BrainOnFire/SNAP_Project_Files/SNAP Project Code/STM32_WPAN/App/custom_app.h

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

/* Define to prevent recursive inclusion -------------------------------------*/
#ifndef CUSTOM_APP_H
#define CUSTOM_APP_H

#ifdef __cplusplus
extern "C" {
#endif

/* Includes ------------------------------------------------------------------*/

/* Exported types ------------------------------------------------------------*/
typedef enum
{
  CUSTOM_CONN_HANDLE_EVT,
  CUSTOM_DISCON_HANDLE_EVT,
} Custom_App_Opcode_Notification_evt_t;

typedef struct
{
  Custom_App_Opcode_Notification_evt_t     Custom_Evt_Opcode;
  uint16_t                                 ConnectionHandle;
} Custom_App_ConnHandle_Not_evt_t;
/* Exported constants --------------------------------------------------------*/
/* External variables --------------------------------------------------------*/
/* USER CODE BEGIN EV */
extern I2C_HandleTypeDef hi2c1;
extern ADC_HandleTypeDef hadc1;
extern IPCC_HandleTypeDef hipcc;
extern RTC_HandleTypeDef hrtc;
extern TIM_HandleTypeDef htim2;
extern float humidity, temperature;
extern uint8_t activador_ble;
extern uint8_t battery_completed;
/* USER CODE END EV */

/* Exported macros ------------------------------------------------------------*/
/* Exported functions ---------------------------------------------*/
void Custom_APP_Init(void);
void Custom_APP_Notification(Custom_App_ConnHandle_Not_evt_t *pNotification);
/* USER CODE BEGIN EF */
extern void ADV_Stop(void);		//Agregado
extern void ADV_Start(void);	//Agregado
/* USER CODE END EF */

#ifdef __cplusplus
}
#endif

#endif /* CUSTOM_APP_H */
